F6ITU/Mentor/Datasheet/case tantalum.jpg

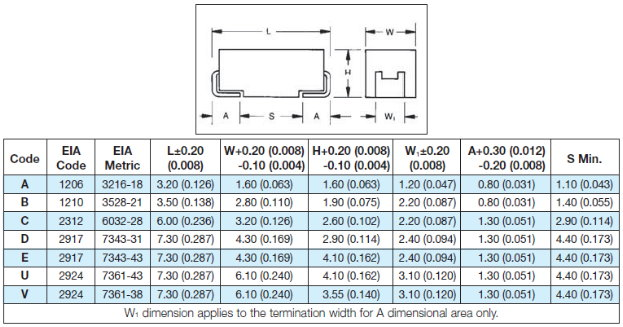
Datasheet/case tantalum.jpg
