F6ITU/Mentor/Datasheet/lcd picture.jpg

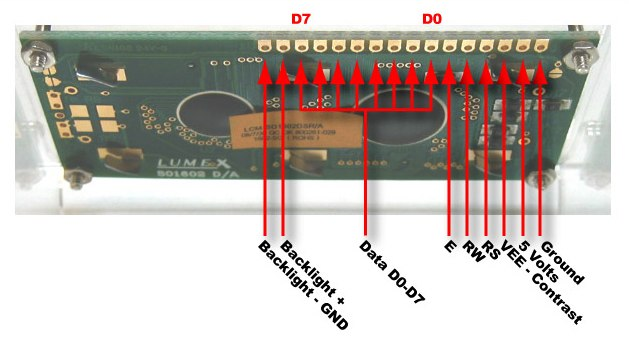
Datasheet/lcd picture.jpg
