F6ITU/Mentor/Datasheet/tantalum cases.PNG

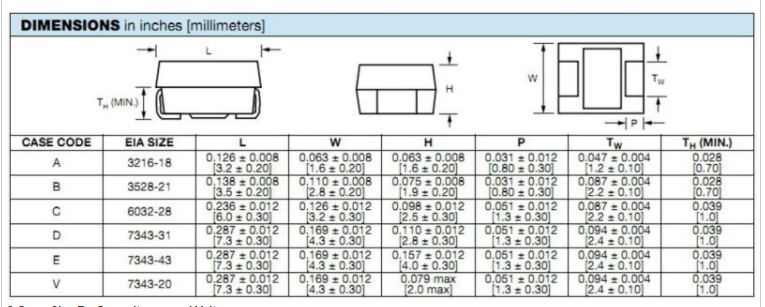
Datasheet/tantalum cases.PNG
