F6ITU/Mentor/Mentor_dwn.jpg

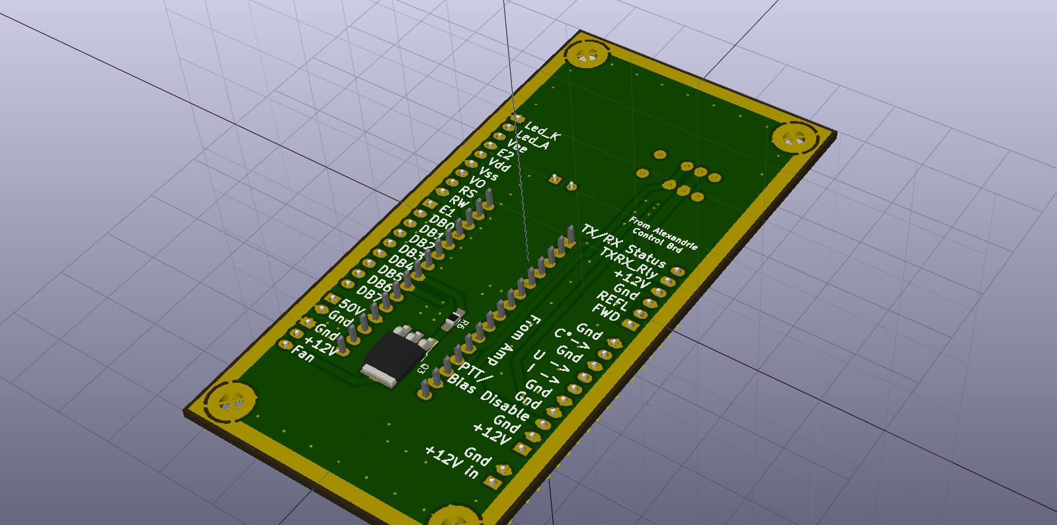
Mentor_dwn.jpg
