F6ITU/Mentor/Modules/2222 3D caract.PNG

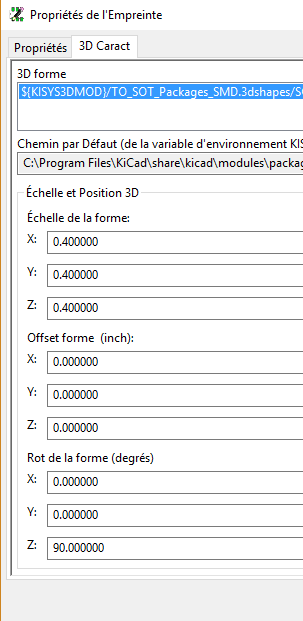
Modules/2222 3D caract.PNG
